LukasGossmann/TinyStepperClock/RP2040/PWM.h

#ifndef PWM_H
#define PWM_H

#include "hardware/irq.h"
#include "pico/types.h"

void seekClockHands(datetime_t *dateTime);
void clear50hzTimerIrq();
void configurePwmAs50hzTimer(irq_handler_t pwmWrapIrqHandler);
void deconfigurePwmFrom50hzTimer(irq_handler_t pwmWrapIrqHandler);

#endif
